jlunaing/Afridev-Hand-Pump-Sensor/docs/img/dm_enclosure.png

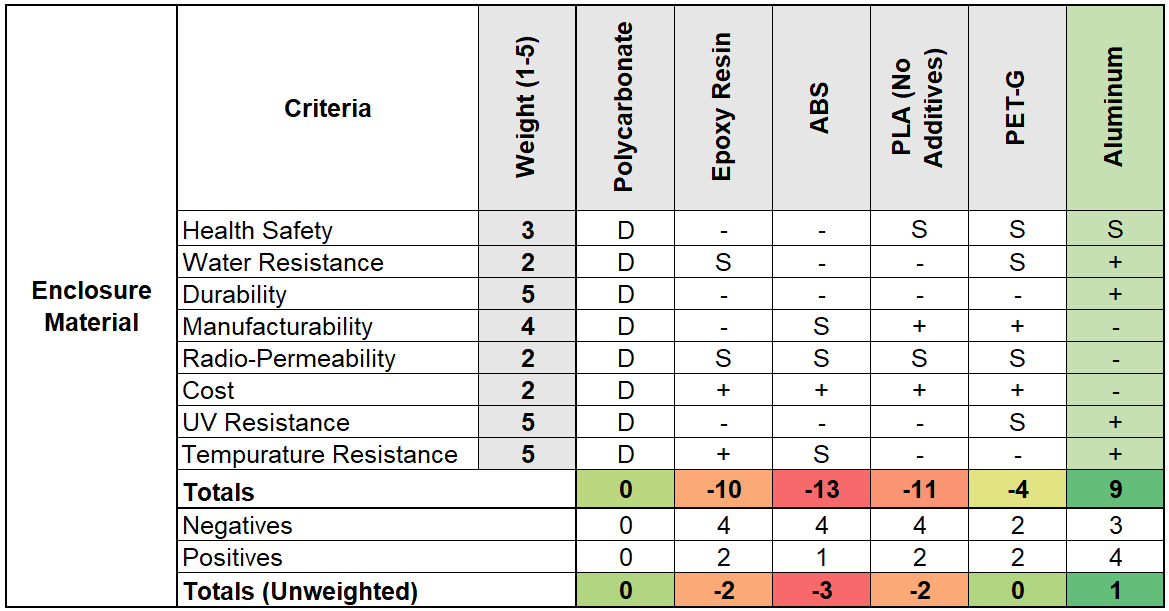
docs/img/dm_enclosure.png
