jlunaing/Afridev-Hand-Pump-Sensor/docs/img/dm_energy_gen.png

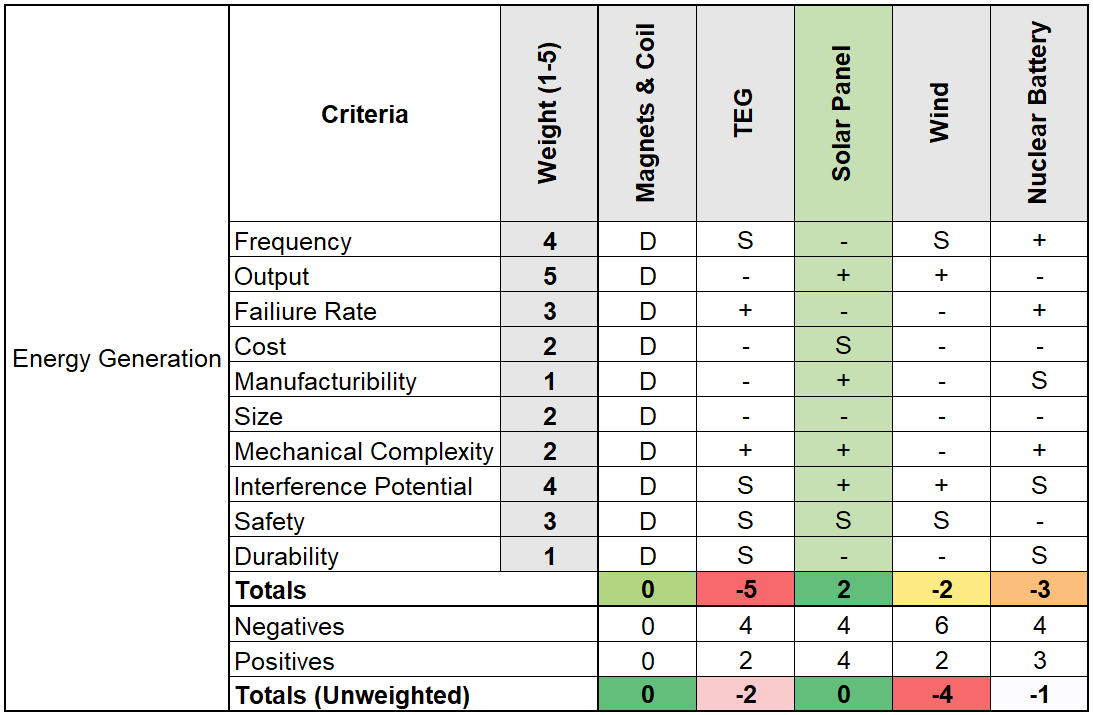
docs/img/dm_energy_gen.png
