jlunaing/Afridev-Hand-Pump-Sensor/docs/img/dm_pumping_act.png

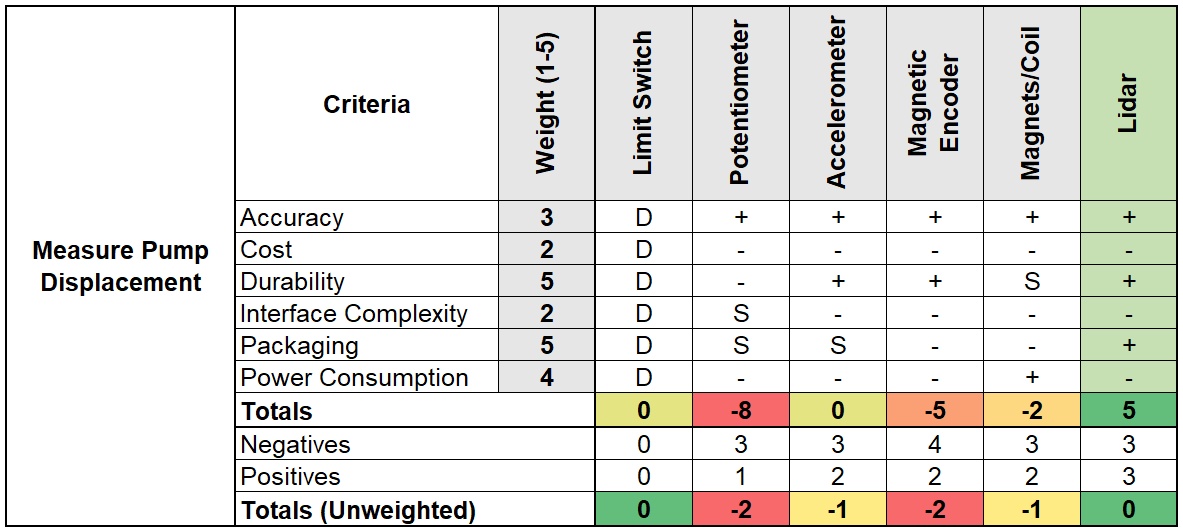
docs/img/dm_pumping_act.png
