jlunaing/Afridev-Hand-Pump-Sensor/hardware/v2/enclosure_bottom.SLDPRT

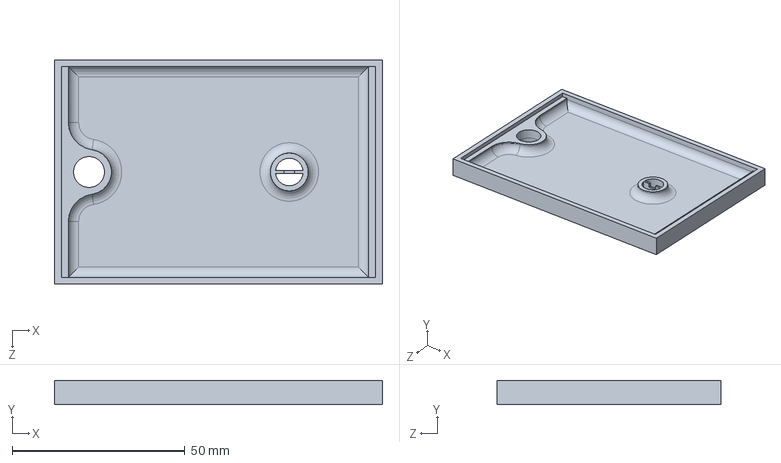
[picture p33: CAD file, 2023-04-22]
hardware/v2/enclosure_bottom.SLDPRT
95.0 x 7.00 x 65.0 mm
