jlunaing/Afridev-Hand-Pump-Sensor/img/v2/assembly_03.png

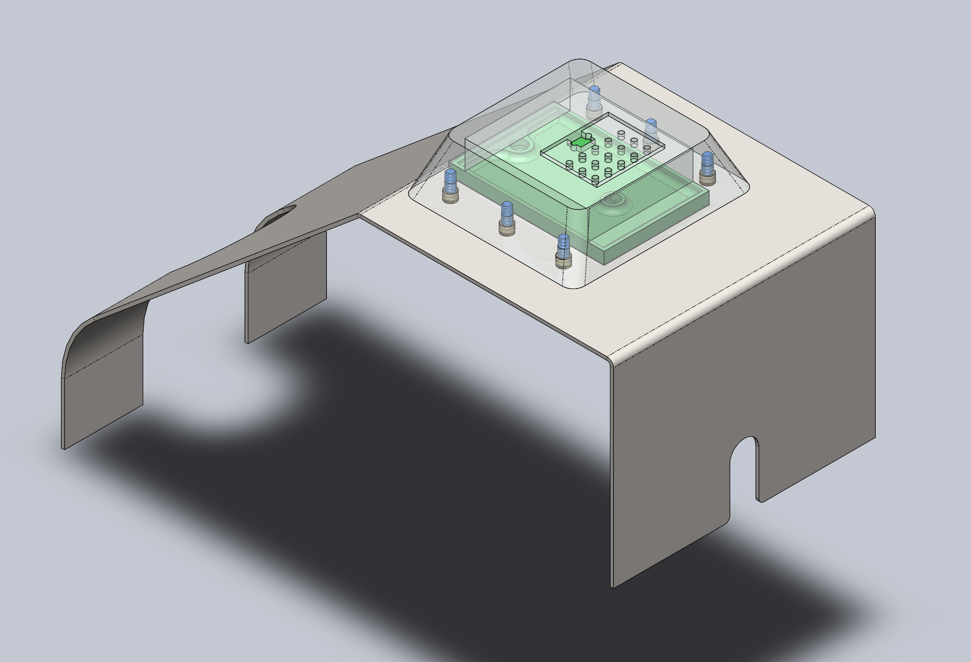
img/v2/assembly_03.png
