jlunaing/Afridev-Hand-Pump-Sensor/img/v2/assembly_05.png

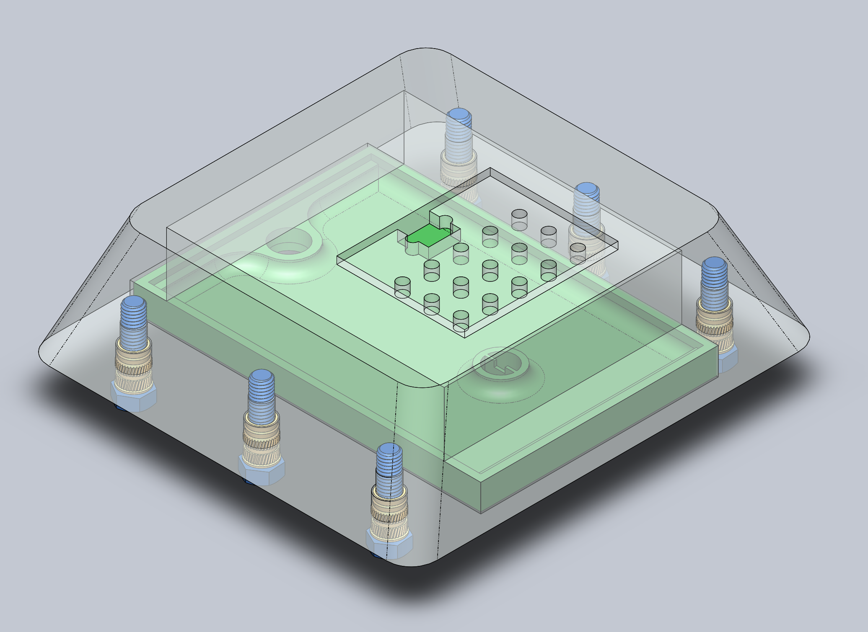
img/v2/assembly_05.png
